devbisme/CAT-Board/docs/Manual/pics/CAT_gerber_pwr.png

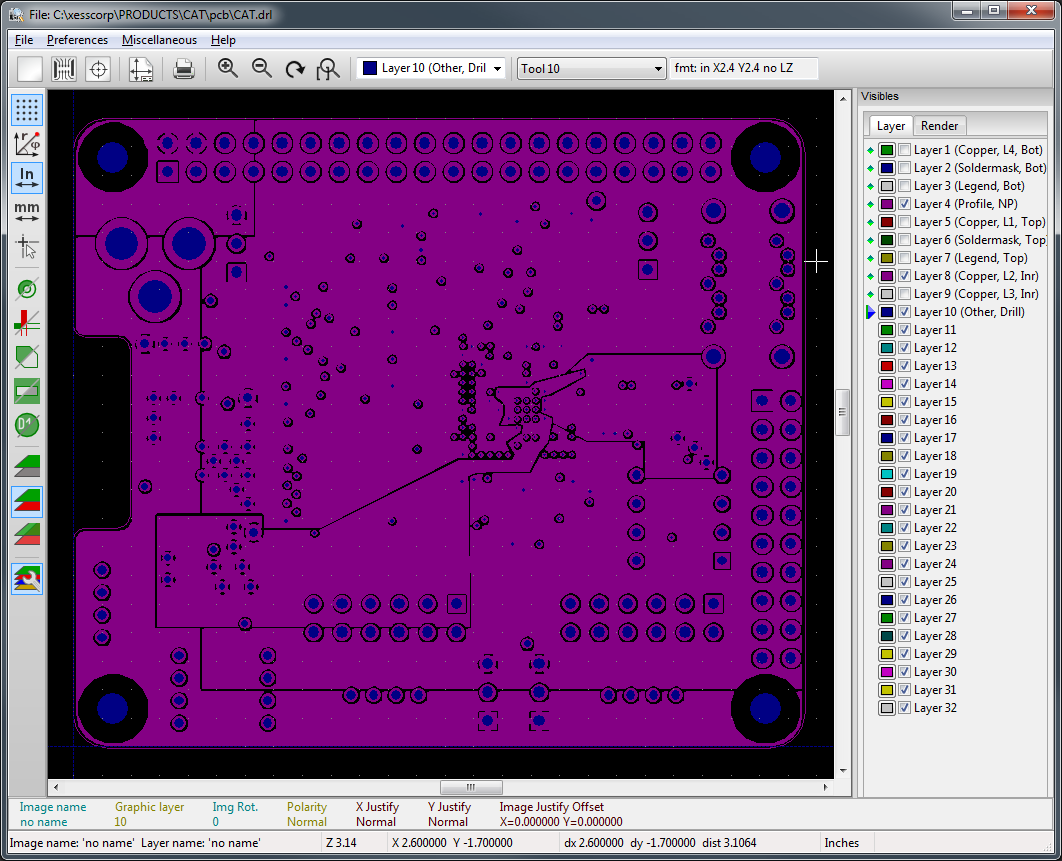
docs/Manual/pics/CAT_gerber_pwr.png
