devbisme/CAT-Board/docs/Manual/pics/CAT_gerber_top.png

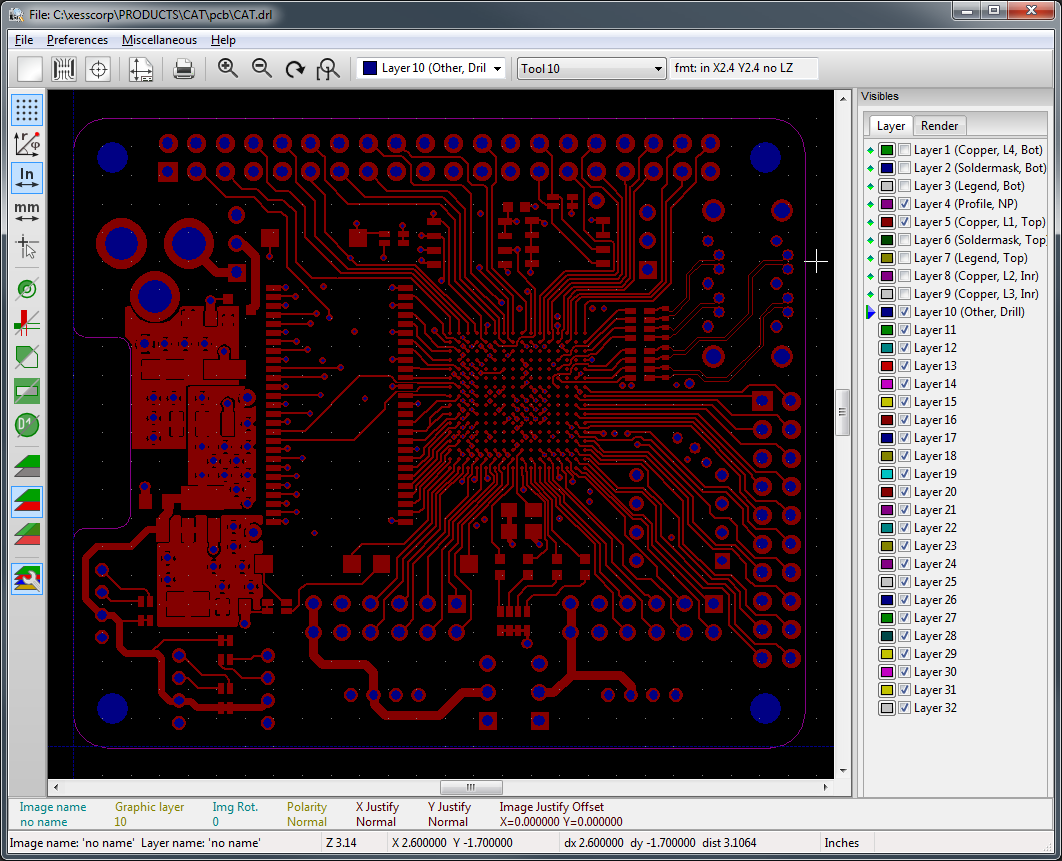
docs/Manual/pics/CAT_gerber_top.png
