devbisme/CAT-Board/docs/Manual/pics/CAT_layout.png

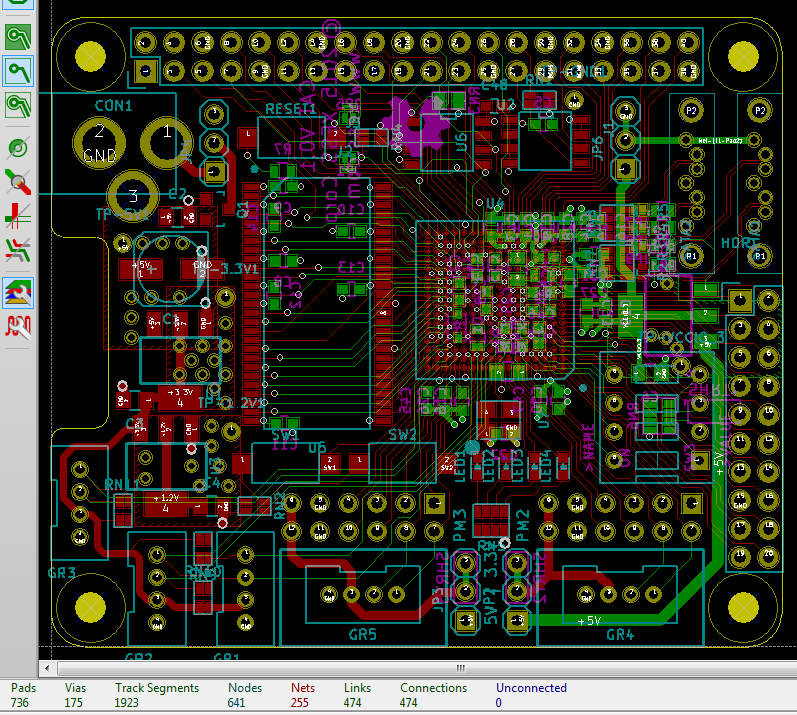
docs/Manual/pics/CAT_layout.png
